lovelypython/lichess-handheld/src/touch.cpp

#include "touch.h"

// v7 also fixes the built-in landscape fallback's horizontally mirrored X axis.
// Old calibration data is intentionally discarded so the corrected sampler and
// the true-landscape display map are calibrated together.
static constexpr uint8_t TOUCH_CAL_VERSION = 7;
static constexpr uint16_t TOUCH_RAW_MIN = 200;
static constexpr uint16_t TOUCH_RAW_MAX = 3900;
static constexpr uint16_t TOUCH_PRESSURE_MIN = 120;
static constexpr uint32_t CAL_TAP_TIMEOUT_MS = 12000;
static constexpr uint32_t CAL_SAMPLE_TIMEOUT_MS = 900;
static constexpr uint32_t CAL_RELEASE_TIMEOUT_MS = 1500;

static uint16_t medianSamples(uint16_t* v, int count) {
  for (int i=0;i<count;i++) for (int j=i+1;j<count;j++) if (v[j]<v[i]) { auto t=v[i];v[i]=v[j];v[j]=t; }
  return v[count/2];
}

void XPT2046Touch::begin() {
  pinMode(PIN_TOUCH_SCK, OUTPUT);
  pinMode(PIN_TOUCH_MOSI, OUTPUT);
  pinMode(PIN_TOUCH_MISO, INPUT);
  pinMode(PIN_TOUCH_CS, OUTPUT);
  pinMode(PIN_TOUCH_IRQ, INPUT_PULLUP);
  digitalWrite(PIN_TOUCH_SCK, LOW);
  digitalWrite(PIN_TOUCH_MOSI, LOW);
  digitalWrite(PIN_TOUCH_CS, HIGH);
  load();
}

uint8_t XPT2046Touch::transfer8(uint8_t value) {
  uint8_t input = 0;
  for (uint8_t mask = 0x80; mask; mask >>= 1) {
    digitalWrite(PIN_TOUCH_SCK, LOW);
    digitalWrite(PIN_TOUCH_MOSI, (value & mask) ? HIGH : LOW);
    delayMicroseconds(TOUCH_SPI_HALF_PERIOD_US);
    digitalWrite(PIN_TOUCH_SCK, HIGH);
    input = uint8_t((input << 1) | (digitalRead(PIN_TOUCH_MISO) ? 1 : 0));
    delayMicroseconds(TOUCH_SPI_HALF_PERIOD_US);
  }
  digitalWrite(PIN_TOUCH_SCK, LOW);
  return input;
}

uint16_t XPT2046Touch::read12(uint8_t command) {
  transfer8(command);
  uint16_t v = (uint16_t(transfer8(0)) << 8) | transfer8(0);
  return (v >> 3) & 0x0FFF;
}

bool XPT2046Touch::readRaw(uint16_t& x, uint16_t& y) {
  // Do not gate reads on T_IRQ. Some XPT2046 boards leave IRQ floating, pulse
  // it too briefly, or hold it low after a noisy transfer. Z1/Z2 are the
  // authoritative press test, while IRQ remains only a useful wake hint.
  uint16_t xs[7], ys[7];
  digitalWrite(PIN_TFT_CS, HIGH);
  digitalWrite(PIN_TOUCH_CS, LOW);
  uint16_t z1 = read12(0xB0);
  for (int i=0;i<7;i++) {
    xs[i] = read12(0xD0);
    ys[i] = read12(0x90);
  }
  uint16_t z2 = read12(0xC0);
  digitalWrite(PIN_TOUCH_CS, HIGH);

  uint16_t pressure = uint16_t(min<uint32_t>(4095, uint32_t(z1) + 4095U - uint32_t(z2)));
  lastPressure_ = pressure;
  if (z1 < 16 || pressure < TOUCH_PRESSURE_MIN) return false;

  x=medianSamples(xs,7); y=medianSamples(ys,7);
  // A real press on this panel stays well away from the ADC rails. 0,0 means
  // IRQ is active but no position data is arriving from XPT2046 T_DO/MISO.
  if (x < 16 || y < 16 || x > 4079 || y > 4079) {
    static uint32_t lastWarningMs = 0;
    if (millis() - lastWarningMs >= 500) {
      Serial.printf("[Touch] invalid raw=%u,%u pressure=%u (check T_DO/MISO, T_CS and power)\n", x, y, pressure);
      lastWarningMs = millis();
    }
    return false;
  }
  return true;
}

TouchPoint XPT2046Touch::read() {
  TouchPoint p;
  uint16_t rx, ry;
  if (!readRaw(rx,ry)) return p;
  p.pressed=true; p.rawX=rx; p.rawY=ry; p.pressure=lastPressure_;
  if (calibrated_) {
    p.x = constrain(int(a_*rx + b_*ry + c_ + 0.5f), 0, SCREEN_W-1);
    p.y = constrain(int(d_*rx + e_*ry + f_ + 0.5f), 0, SCREEN_H-1);
  }
  return p;
}

void XPT2046Touch::load() {
  prefs_.begin("touch", false);
  calibrated_ = prefs_.getBool("ok", false) &&
                prefs_.getUChar("ver", 0) == TOUCH_CAL_VERSION;
  usingDefaultCalibration_ = prefs_.getBool("fallback", false);
  a_=prefs_.getFloat("a",0); b_=prefs_.getFloat("b",0); c_=prefs_.getFloat("c",0);
  d_=prefs_.getFloat("d",0); e_=prefs_.getFloat("e",0); f_=prefs_.getFloat("f",0);
  calibrated_ = calibrated_ && isfinite(a_) && isfinite(b_) && isfinite(c_) &&
                isfinite(d_) && isfinite(e_) && isfinite(f_);
  if (!calibrated_) usingDefaultCalibration_ = false;
  prefs_.end();
}
void XPT2046Touch::save() {
  prefs_.begin("touch", false);
  prefs_.putBool("ok", true);
  prefs_.putUChar("ver", TOUCH_CAL_VERSION);
  prefs_.putBool("fallback", usingDefaultCalibration_);
  prefs_.putFloat("a",a_); prefs_.putFloat("b",b_); prefs_.putFloat("c",c_);
  prefs_.putFloat("d",d_); prefs_.putFloat("e",e_); prefs_.putFloat("f",f_);
  prefs_.end();
}
void XPT2046Touch::clearCalibration() {
  prefs_.begin("touch", false); prefs_.clear(); prefs_.end();
  calibrated_=false;
  usingDefaultCalibration_=false;
}

void XPT2046Touch::useDefaultCalibration(bool persist) {
  // MSP4021/XPT2046 landscape fallback for this exact mounting:
  // touch Y drives the INVERTED screen X axis, while touch X drives the
  // inverted screen Y axis. The old positive X slope mirrored all left/right
  // controls (Puzzle -> Online, Back -> Confirm).
  const float rawSpan = float(TOUCH_RAW_MAX - TOUCH_RAW_MIN);
  a_ = 0.0f;
  b_ = -float(SCREEN_W - 1) / rawSpan;
  c_ = float(SCREEN_W - 1) - b_ * TOUCH_RAW_MIN;
  d_ = -float(SCREEN_H - 1) / rawSpan;
  e_ = 0.0f;
  f_ = float(SCREEN_H - 1) - d_ * TOUCH_RAW_MIN;
  calibrated_ = true;
  usingDefaultCalibration_ = true;
  if (persist) save();
  Serial.println("[Touch] built-in default calibration enabled (X/Y inverted landscape map)");
}

static float det3(const float m[3][3]) {
  return m[0][0]*(m[1][1]*m[2][2]-m[1][2]*m[2][1])
       - m[0][1]*(m[1][0]*m[2][2]-m[1][2]*m[2][0])
       + m[0][2]*(m[1][0]*m[2][1]-m[1][1]*m[2][0]);
}
static bool solve3(const float A[3][3], const float Y[3], float out[3]) {
  float det=det3(A); if (fabs(det)<1e-6f) return false;
  for(int col=0;col<3;col++){
    float M[3][3];
    for(int r=0;r<3;r++)for(int c=0;c<3;c++)M[r][c]=(c==col)?Y[r]:A[r][c];
    out[col]=det3(M)/det;
  }
  return true;
}

bool XPT2046Touch::solveAffine(const float raw[][2], const float scr[][2], size_t count) {
  if(count<3)return false;
  float A[3][3]={{0,0,0},{0,0,0},{0,0,0}},X[3]={0,0,0},Y[3]={0,0,0};
  for(size_t i=0;i<count;i++){
    const float v[3]={raw[i][0],raw[i][1],1.0f};
    for(int r=0;r<3;r++){
      X[r]+=v[r]*scr[i][0];Y[r]+=v[r]*scr[i][1];
      for(int c=0;c<3;c++)A[r][c]+=v[r]*v[c];
    }
  }
  float ox[3], oy[3];
  if(!solve3(A,X,ox)||!solve3(A,Y,oy)) return false;
  a_=ox[0]; b_=ox[1]; c_=ox[2]; d_=oy[0]; e_=oy[1]; f_=oy[2];
  float maxError=0;
  for(size_t i=0;i<count;i++){
    float px=a_*raw[i][0]+b_*raw[i][1]+c_;
    float py=d_*raw[i][0]+e_*raw[i][1]+f_;
    float dx=px-scr[i][0],dy=py-scr[i][1];
    maxError=max(maxError,sqrtf(dx*dx+dy*dy));
  }
  return isfinite(maxError)&&maxError<=70.0f;
}

static void drawTarget(ST7796Display& tft,int x,int y) {
  uint16_t bg=ST7796Display::rgb565(18,20,24), fg=ST7796Display::rgb565(255,176,32);
  tft.fillScreen(bg);
  tft.drawLine(x-26,y,x+26,y,fg);
  tft.drawLine(x,y-26,x,y+26,fg);
  tft.drawCircle(x,y,24,fg);
  tft.drawCircle(x,y,16,fg);
  tft.drawText(10,10,"Touch calibration",ST7796Display::rgb565(255,255,255),bg,2);
  tft.drawText(10,294,"Tap anywhere inside the orange circle",ST7796Display::rgb565(210,210,210),bg,1);
}

void XPT2046Touch::runCalibration(ST7796Display& tft) {
  const float scr[5][2]={{48,48},{SCREEN_W-48,48},{SCREEN_W-48,SCREEN_H-48},
                         {48,SCREEN_H-48},{SCREEN_W/2.0f,SCREEN_H/2.0f}};
  float raw[5][2];
  bool captureFailed=false;
  for(int i=0;i<5;i++){
    drawTarget(tft,int(scr[i][0]),int(scr[i][1]));
    uint32_t waitStarted=millis();
    uint16_t firstX=0,firstY=0;
    bool pressed=false;
    while(millis()-waitStarted<CAL_TAP_TIMEOUT_MS){
      if(readRaw(firstX,firstY)){pressed=true;break;}
      delay(8);
    }
    if(!pressed){captureFailed=true;break;}
    uint16_t xs[15],ys[15];int n=0;uint16_t capturedPressure=lastPressure_;
    xs[n]=firstX;ys[n]=firstY;n++;
    uint32_t sampleStarted=millis();
    while(n<15&&millis()-sampleStarted<CAL_SAMPLE_TIMEOUT_MS){
      uint16_t x,y;
      if(!readRaw(x,y))break;
      xs[n]=x;ys[n]=y;n++;capturedPressure=lastPressure_;
      delay(4);
    }
    uint32_t releaseStarted=millis();
    int releasedSamples=0;
    while(millis()-releaseStarted<CAL_RELEASE_TIMEOUT_MS&&releasedSamples<3){
      uint16_t x,y;
      if(readRaw(x,y))releasedSamples=0;else releasedSamples++;
      delay(8);
    }
    if(n<3||releasedSamples<3){captureFailed=true;break;}
    raw[i][0]=medianSamples(xs,n);raw[i][1]=medianSamples(ys,n);
    Serial.printf("[Touch] calibration %d/5 raw=%d,%d pressure=%u\n",i+1,int(raw[i][0]),int(raw[i][1]),capturedPressure);
    delay(100);
  }
  calibrated_=!captureFailed&&solveAffine(raw,scr,5);
  if(calibrated_){usingDefaultCalibration_=false;save();}
  else useDefaultCalibration(true);
  tft.fillScreen(ST7796Display::rgb565(18,20,24));
  if(usingDefaultCalibration_){
    tft.drawText(24,125,"Calibration failed",ST7796Display::rgb565(255,176,32),ST7796Display::rgb565(18,20,24),2);
    tft.drawText(24,160,"Using default touch map",ST7796Display::rgb565(80,220,120),ST7796Display::rgb565(18,20,24),2);
  }else{
    tft.drawText(24,140,"Touch calibrated",ST7796Display::rgb565(80,220,120),ST7796Display::rgb565(18,20,24),2);
  }
  delay(1400);
}
