lovelypython/lichess-handheld/include/pieces_user.h

#pragma once
#include <Arduino.h>
#define USER_PIECES_AVAILABLE 1
static constexpr int USER_PIECE_W=36;
static constexpr int USER_PIECE_H=36;
static const uint16_t wp_pix[1296] PROGMEM={
0x0000,0x0000,0x0000,0x0000,0x0000,0x0000,0x0000,0x0000,0x0000,0x0000,0x0000,0x0000,0xFFFF,0x52AA,0x0000,0x0000,0x0000,0x0000,
0x0000,0x0000,0x0000,0x52AA,0xFFFF,0x0000,0x0000,0x0000,0x0000,0x0000,0x0000,0x0000,0x0000,0x0000,0x0000,0x0000,0x0000,0x0000,
0x0000,0x0000,0x0000,0x0000,0x0000,0x0000,0x0000,0x0000,0x0000,0x0000,0x0000,0xFFFF,0x0000,0x0000,0xFFFE,0x9490,0x7BCD,0x8C2F,
0x7BCD,0x9CD1,0xFFFF,0x0000,0x0000,0x0000,0x0000,0x0000,0x0000,0x0000,0x0000,0x0000,0x0000,0x0000,0x0000,0x0000,0x0000,0x0000,
0x0000,0x0000,0x0000,0x0000,0x0000,0x0000,0x0000,0x0000,0x0000,0x0000,0xFFFF,0x0000,0xFFFF,0xA532,0x632B,0x62EB,0x6B4C,0x738E,
0x738E,0x630B,0x6B4B,0xAD73,0xFFFF,0x52AA,0xFFFF,0x0000,0x0000,0x0000,0x0000,0x0000,0x0000,0x0000,0x0000,0x0000,0x0000,0x0000,
0x0000,0x0000,0x0000,0x0000,0x0000,0x0000,0x0000,0x0000,0x0000,0xFFFF,0x7BEF,0xFFFF,0x9CD1,0x5AEB,0x8C71,0xEF7D,0xFFFF,0xFFFF,
0xFFFF,0xE73C,0x9471,0x62EB,0x9CF1,0x0000,0xFFFF,0x0000,0x0000,0x0000,0x0000,0x0000,0x0000,0x0000,0x0000,0x0000,0x0000,0x0000,
0x0000,0x0000,0x0000,0x0000,0x0000,0x0000,0x0000,0x0000,0x0000,0xFBEF,0x0000,0xA512,0x5ACA,0xB5B6,0xFFFF,0xFFFF,0xFFFF,0xFFFF,
0xFFDF,0xFFFF,0xFFFF,0xA4F3,0x5AAA,0xA532,0x0000,0xAD4A,0x0000,0x0000,0x0000,0x0000,0x0000,0x0000,0x0000,0x0000,0x0000,0x0000,
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
    case 'R': return wr_mask;
    case 'Q': return wq_mask;
    case 'K': return wk_mask;
    case 'p': return bp_mask;
    case 'n': return bn_mask;
    case 'b': return bb_mask;
    case 'r': return br_mask;
    case 'q': return bq_mask;
    case 'k': return bk_mask;
  } return nullptr; }
