lovelypython/lichess-handheld/include/tls_root.h

#pragma once
// ISRG Root X2 (ECDSA P-384). TLS is validated; setInsecure() is never used.
// Lichess is served through Cloudflare's ECDSA certificate chain. Using X2
// avoids the ESP32-C5/IDF 5.5.5 hardware-MPI assertion seen while verifying
// the 4096-bit RSA ISRG Root X1 chain.
static constexpr const char LICHESS_ROOT_CA[] PROGMEM = R"EOF(
-----BEGIN CERTIFICATE-----
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
/q4AaOeMSQ+2b1tbFfLn
-----END CERTIFICATE-----
)EOF";
